kaz-mac/fir-rack/shelf/template/depth_130mm/2U Shelf.stl

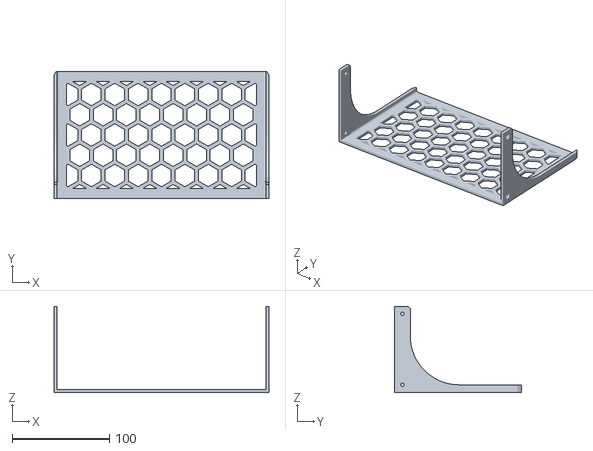
[picture p17: CAD file, 2026-09-07]
shelf/template/depth_130mm/2U Shelf.stl
220.8 x 130.0 x 88.5
