kaz-mac/fir-rack/shelf/template/depth_195mm/1U Shelf.stl

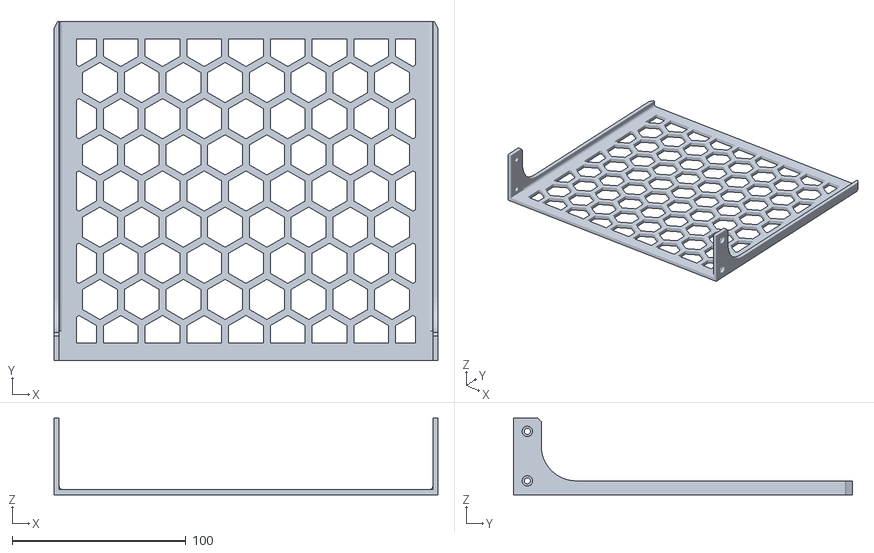
[picture p18: CAD file, 2026-09-07]
shelf/template/depth_195mm/1U Shelf.stl
220.8 x 195.0 x 44.0
