kaz-mac/fir-rack/shelf/template/depth_195mm/1U Ear.stl

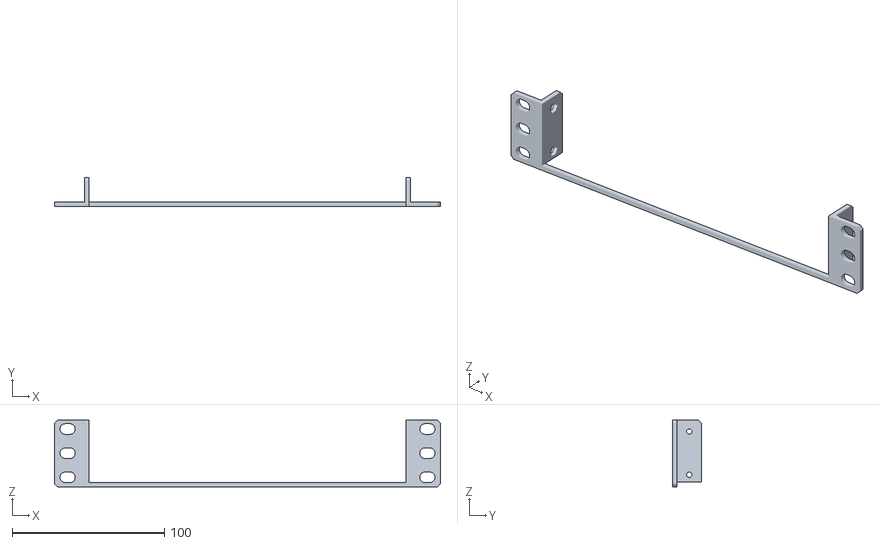
[picture p19: CAD file, 2026-09-07]
shelf/template/depth_195mm/1U Ear.stl
253.8 x 19.0 x 44.0
