kaz-mac/fir-rack/shelf/template/depth_260mm/1U Shelf.stl

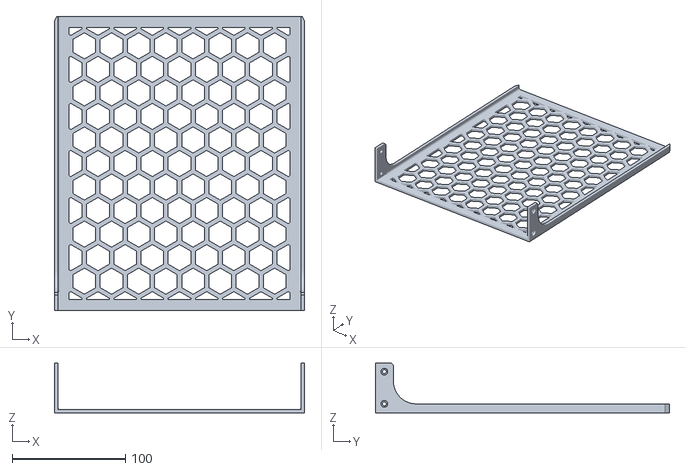
[picture p20: CAD file, 2026-09-07]
shelf/template/depth_260mm/1U Shelf.stl
220.8 x 260.0 x 44.0
