kaz-mac/fir-rack/shelf/template/depth_130mm/130mm.3mf

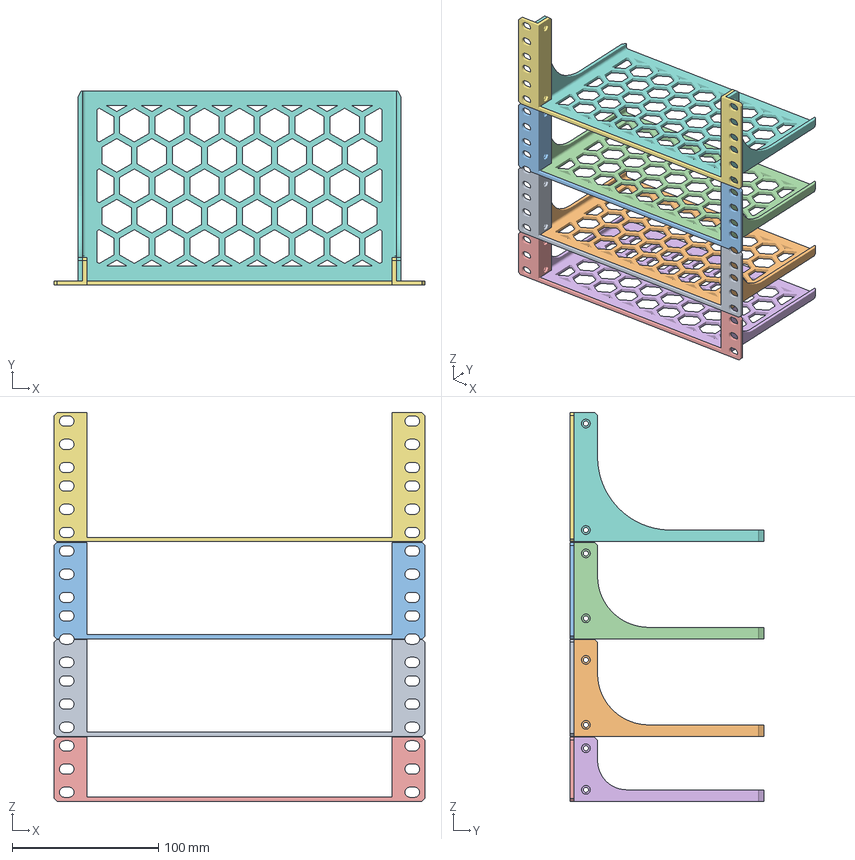
[picture p22: CAD file, 2026-09-07]
shelf/template/depth_130mm/130mm.3mf
253.8 x 133.0 x 266.3 mm
1.5U-DW Ear
1.5U-DW Shelf
1.5U-UP Ear
1.5U-UP Shelf
1U Ear
1U Shelf
2U Ear
2U Shelf
