kaz-mac/fir-rack/shelf/template/depth_256mm/1U Shelf.stl

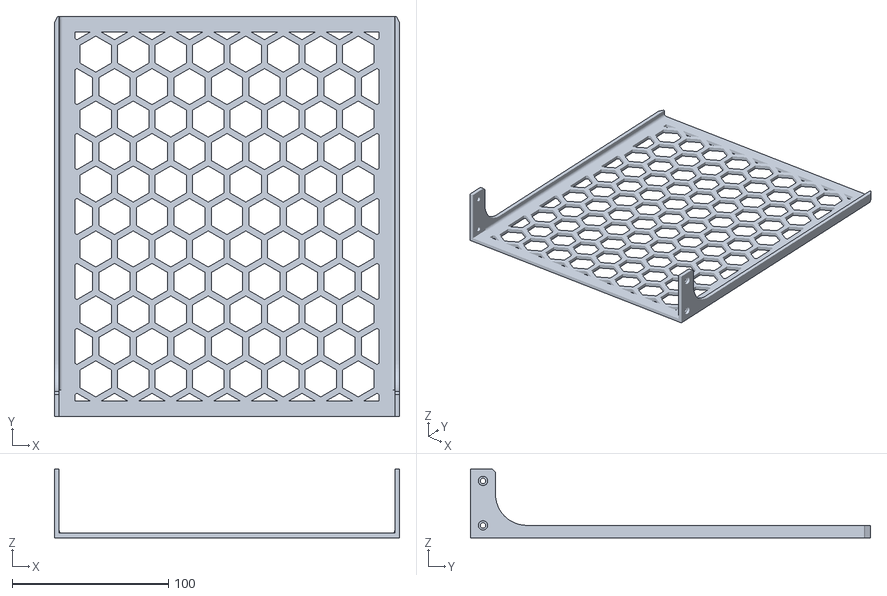
[picture p23: CAD file, 2026-09-07]
shelf/template/depth_256mm/1U Shelf.stl
220.8 x 256.0 x 44.0
