kaz-mac/fir-rack/shelf/template/depth_195mm/1.5U-UP Shelf.stl

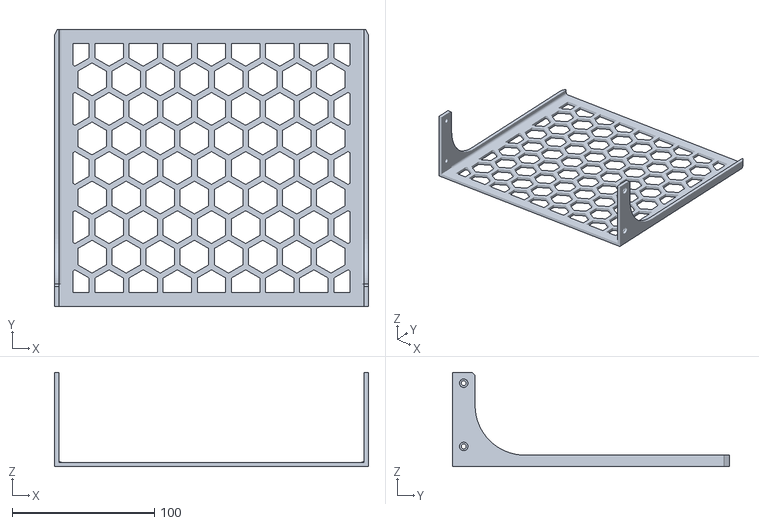
[picture p25: CAD file, 2026-09-07]
shelf/template/depth_195mm/1.5U-UP Shelf.stl
220.8 x 195.0 x 66.1
