kaz-mac/fir-rack/shelf/template/depth_260mm/1.5U-UP Shelf.stl

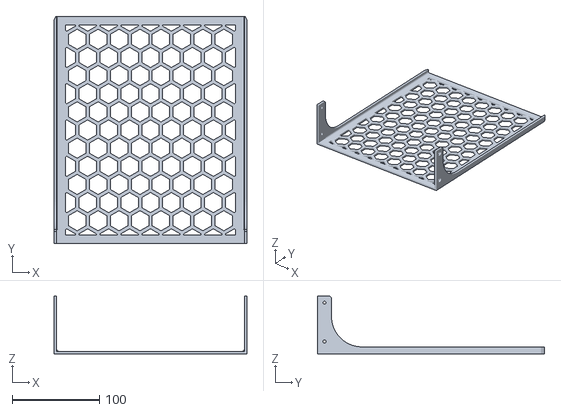
[picture p27: CAD file, 2026-09-07]
shelf/template/depth_260mm/1.5U-UP Shelf.stl
220.8 x 260.0 x 66.1
